askanuradha/Air-Quality-Monitoring-Device/Enclosure/Dust sensor GP2Y1010AU0F.step

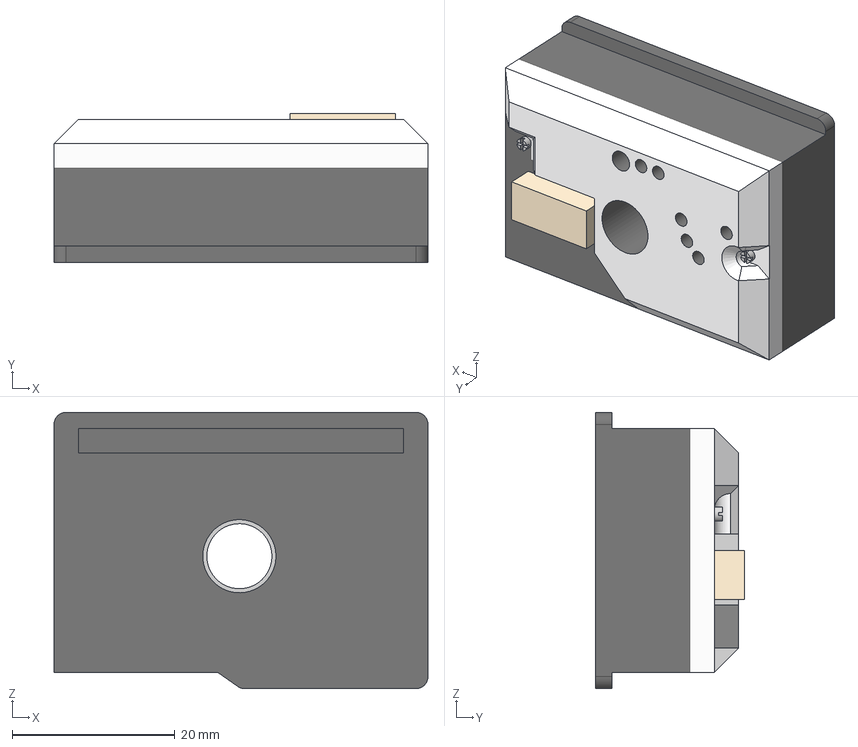
[picture p19: CAD file, 2023-09-05]
Enclosure/Dust sensor GP2Y1010AU0F.step
46.0 x 18.3 x 34.0 mm
