askanuradha/Air-Quality-Monitoring-Device/Enclosure/KY-015.step

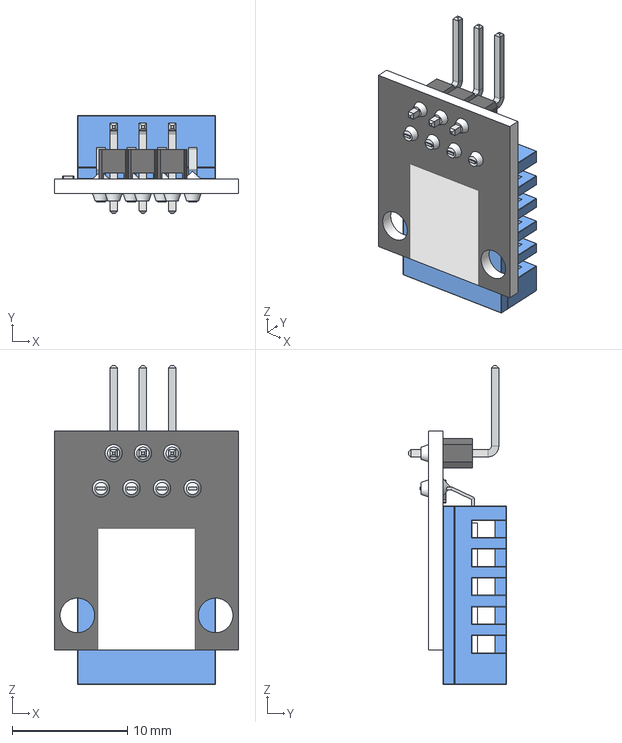
[picture p21: CAD file, 2023-09-05]
Enclosure/KY-015.step
16.0 x 8.50 x 27.7 mm
