askanuradha/Air-Quality-Monitoring-Device/PCB/Imports/header-23.snapshot.38/header7pin.stp

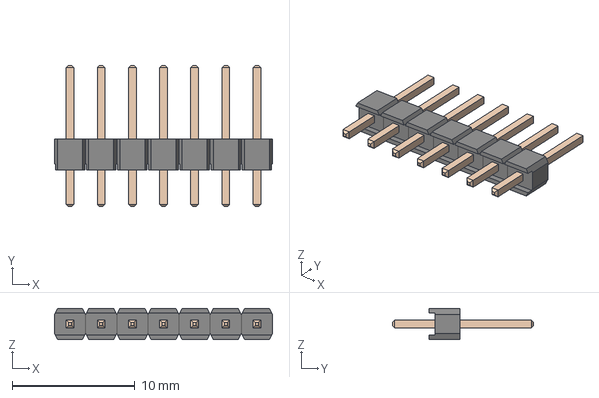
[picture p29: CAD file, 2023-09-05]
PCB/Imports/header-23.snapshot.38/header7pin.stp
17.8 x 11.5 x 2.54 mm
6130xx11121_PIN x 7
