askanuradha/Air-Quality-Monitoring-Device/PCB/Imports/header-23.snapshot.38/header16pin.stp

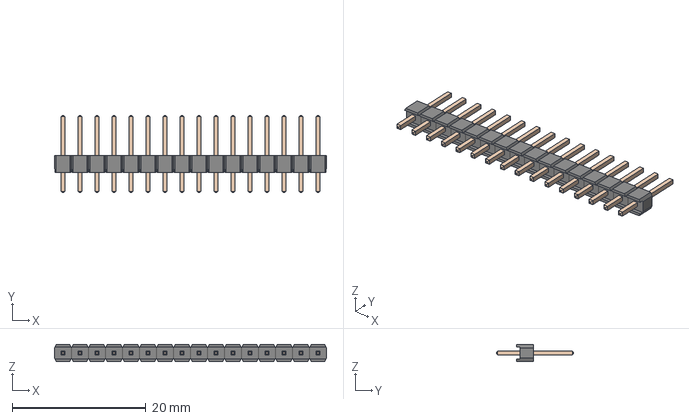
[picture p31: CAD file, 2023-09-05]
PCB/Imports/header-23.snapshot.38/header16pin.stp
40.6 x 11.5 x 2.54 mm
6130xx11121_PIN x 16
